jeffqchen/TwinDiamond-Twin-Famicom-Expansion-to-NES-SNES-Controller-Adapter/Pics/09.jpg

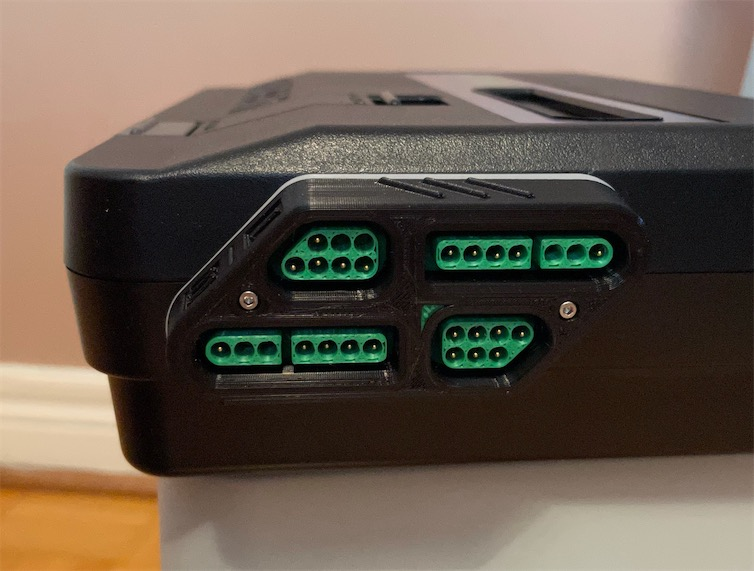
Pics/09.jpg
